PontshoMbizo/SRAM_sampling/firmware/simulations/src/read.v

module read(
    input wire E,            // Chip Enable
    input wire O,            // Output Enable
    input wire [3:0] counter, // timing value
    output reg read          // Output signal to indicate read mode
);    
    always @(*) begin
        if (~E && ~O && counter >= 4'd14) begin // Check if chip is enabled and counter is at least 14
            read <= 1;
        end 
		  else begin
            read <= 0;
        end
    end
endmodule
